LukasT03/LTS-Respooler/3D Files/STLs V4/Tension Holder 1.stl

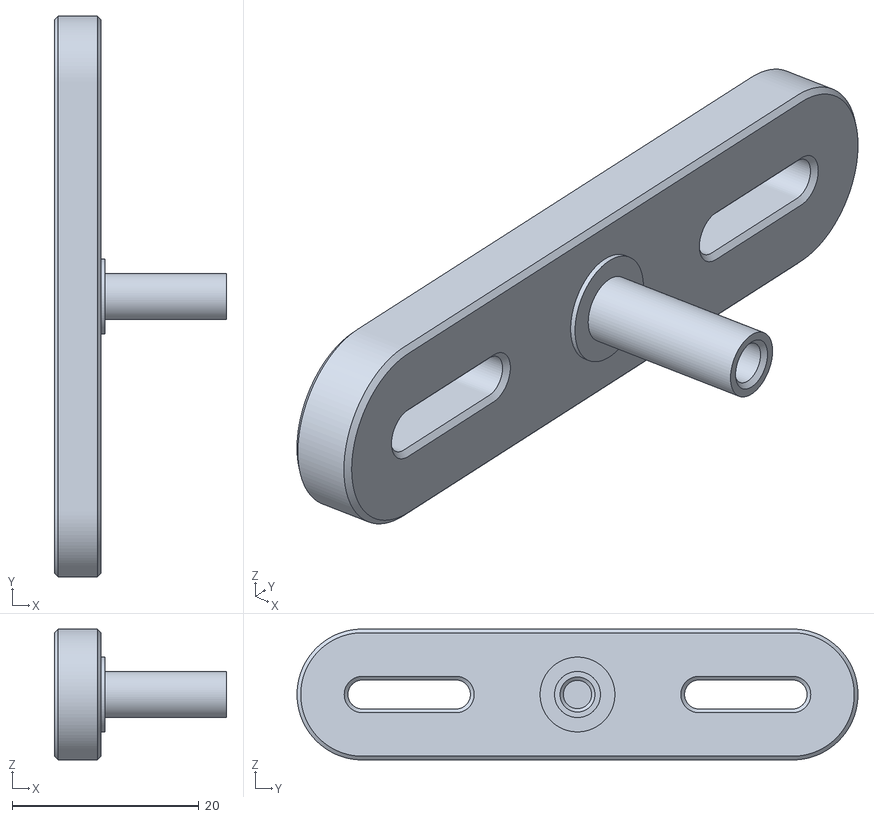
[picture p15: CAD file, 2025-08-27]
3D Files/STLs V4/Tension Holder 1.stl
18.4 x 60.0 x 14.0
