LukasT03/LTS-Respooler/Print Profiles/Control Panel (single color).3mf

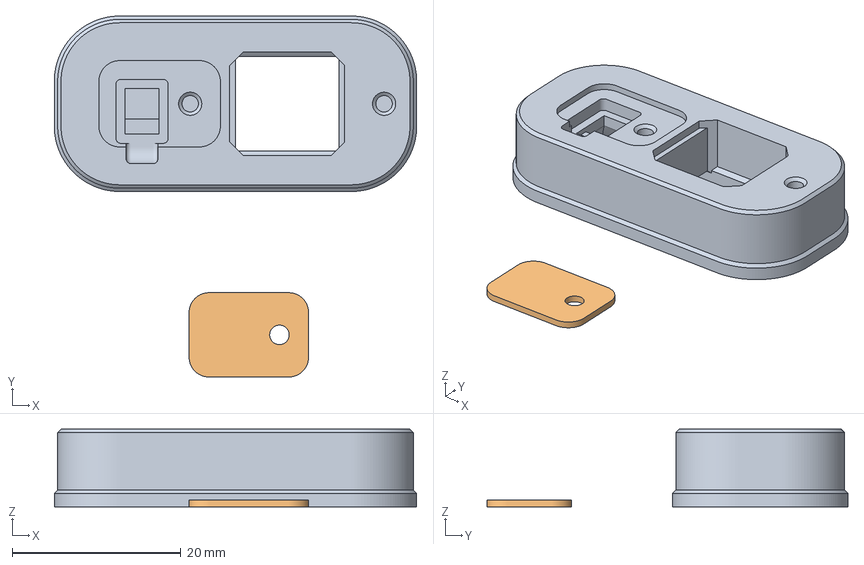
[picture p16: CAD file, 2025-09-30]
Print Profiles/Control Panel (single color).3mf
43.0 x 42.8 x 9.20 mm
Control Panel Single Color.stl
Control Panel Plate.stl
