LukasT03/LTS-Respooler/3D Files/STLs Pro/Control Panel Plate.stl

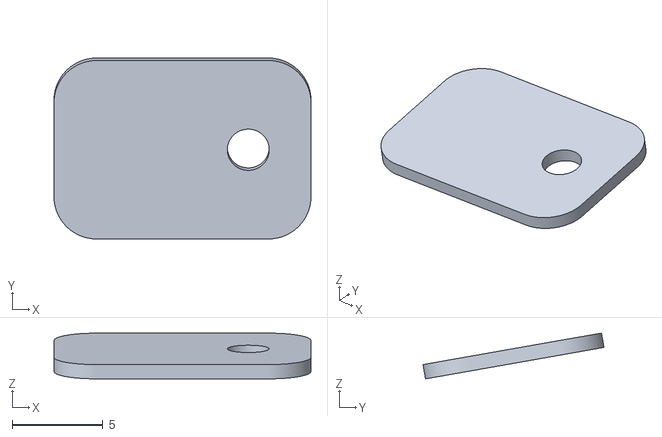
[picture p17: CAD file, 2025-09-09]
3D Files/STLs Pro/Control Panel Plate.stl
14.2 x 9.99 x 2.52
