LukasT03/LTS-Respooler/3D Files/STLs V4/Guide Pulley.stl

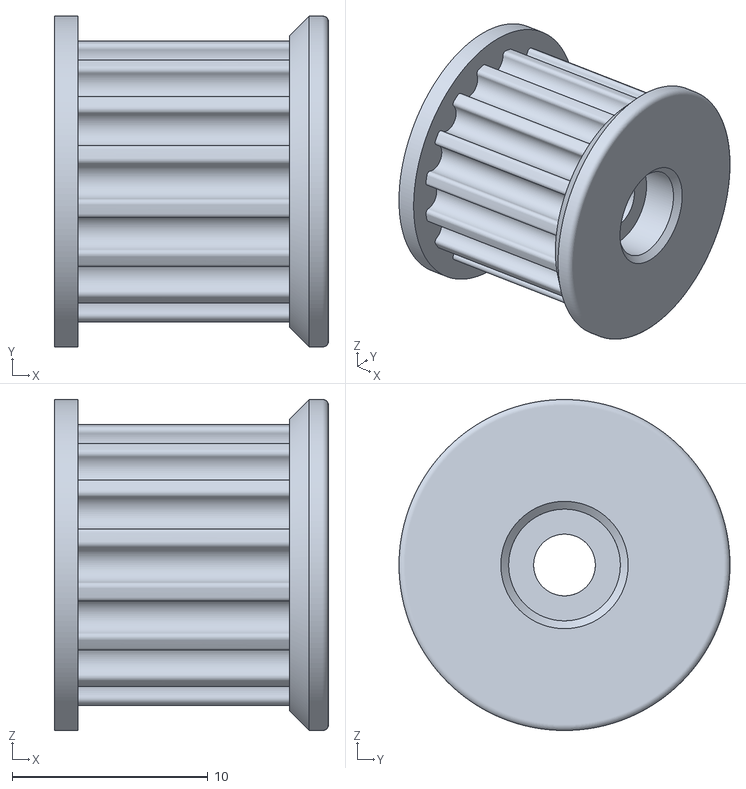
[picture p18: CAD file, 2025-08-24]
3D Files/STLs V4/Guide Pulley.stl
14.0 x 16.9 x 16.9
