LukasT03/LTS-Respooler/Print Profiles/LTS Respooler (V3).3mf

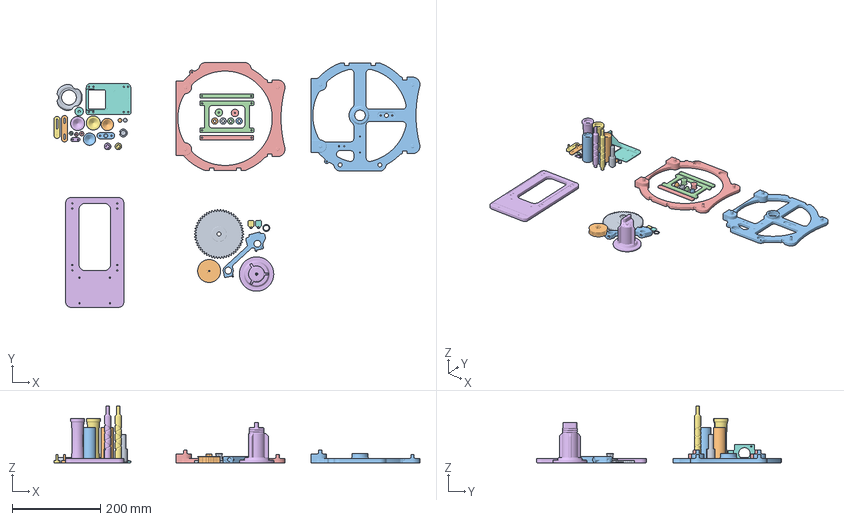
[picture p19: CAD file, 2025-08-23]
Print Profiles/LTS Respooler (V3).3mf
830.6 x 555.6 x 128.4 mm
Spool nut.stl
bottom Roller.stl x 2
Brace single.stl x 2
Spool center.stl
Filament guide lid.stl x 2
Filament guide pins.stl x 2
Filament guide.stl
Brace double.stl
Frame L.stl
Base.stl
top Roller.stl x 2
washer Spool shaft.stl
big Gear V3.stl
small Gear V3.stl
Frame R V3.stl
Guide Pulley V3.stl x 2
Worm gear V3.stl x 2
Motor Base V3.stl
Spool shaft V3.stl
Tension holder 1.stl
Gear shaft.stl
Tension washer 1.stl x 2
Tension washer 2.stl
Tension holder 2.stl
Motor Pulley.stl
Tension Pulley 1.stl x 2
Tension Pulley 2.stl x 2
Bearing washer.stl
