LukasT03/LTS-Respooler/3D Files/STLs Pro/Control Panel Multi Color 1.stl

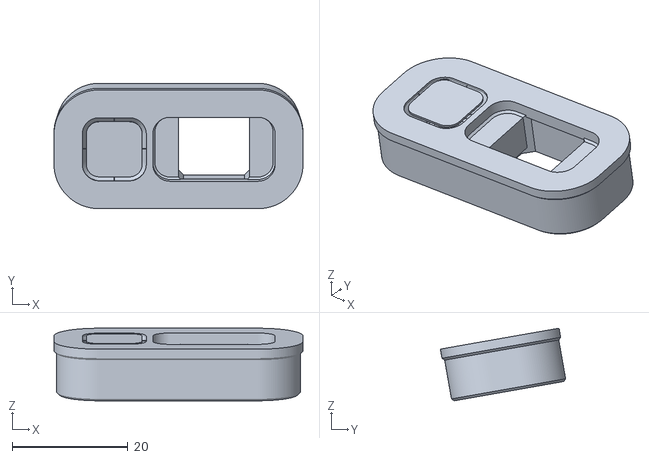
[picture p20: CAD file, 2025-09-09]
3D Files/STLs Pro/Control Panel Multi Color 1.stl
43.0 x 21.6 x 12.5
