LukasT03/LTS-Respooler/3D Files/STLs V4/Small Gear.stl

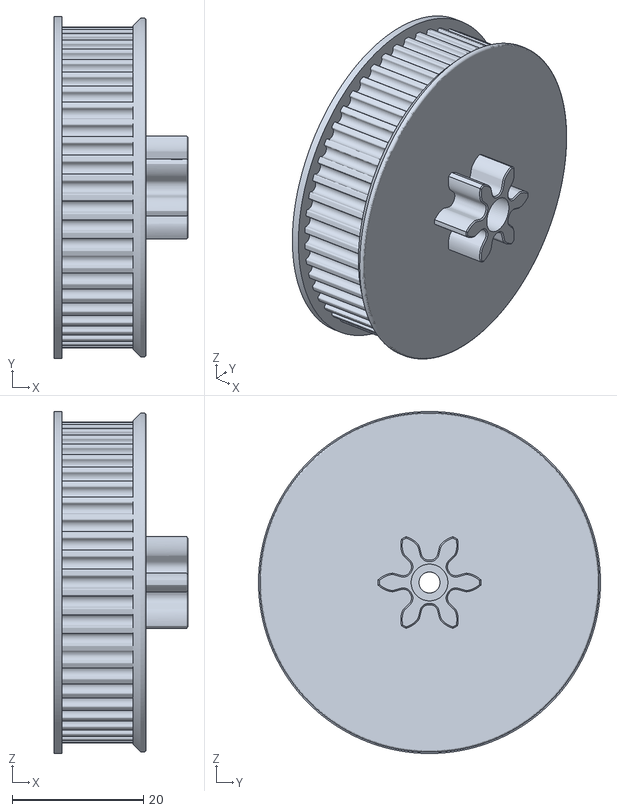
[picture p21: CAD file, 2025-08-24]
3D Files/STLs V4/Small Gear.stl
20.4 x 52.1 x 52.1
