LukasT03/LTS-Respooler/3D Files/STLs V4/Spool Shaft.stl

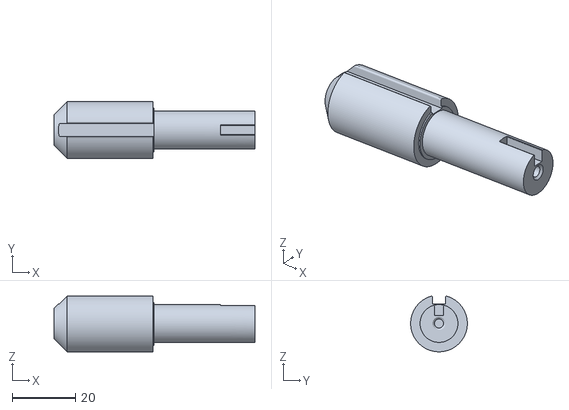
[picture p22: CAD file, 2025-08-24]
3D Files/STLs V4/Spool Shaft.stl
63.8 x 18.0 x 17.7
