LukasT03/LTS-Respooler/3D Files/STLs Pro/Tension Holder.stl

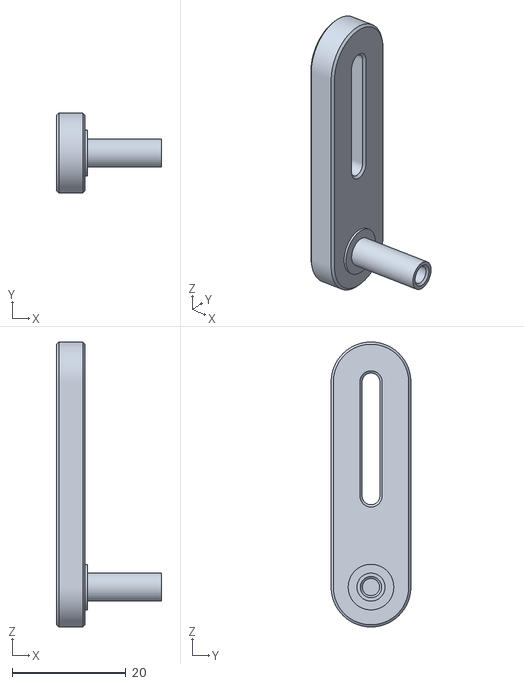
[picture p23: CAD file, 2025-08-27]
3D Files/STLs Pro/Tension Holder.stl
18.4 x 14.0 x 50.0
