LukasT03/LTS-Respooler/3D Files/STLs V4/Gear Shaft.stl

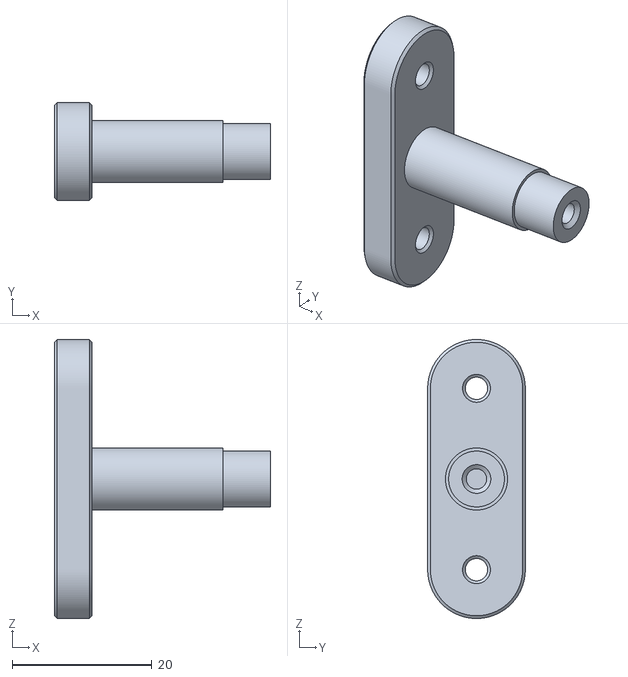
[picture p24: CAD file, 2025-08-24]
3D Files/STLs V4/Gear Shaft.stl
31.0 x 14.0 x 40.0
