LukasT03/LTS-Respooler/3D Files/STLs Pro/Motor Base.stl

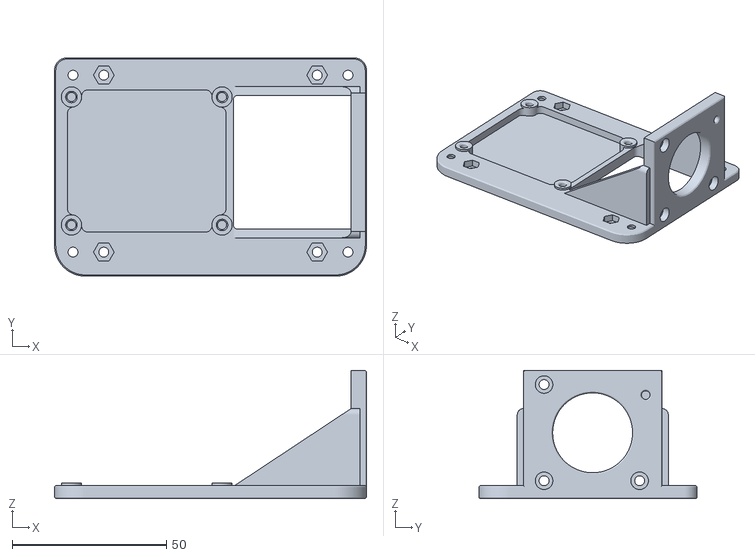
[picture p25: CAD file, 2025-08-25]
3D Files/STLs Pro/Motor Base.stl
101.2 x 70.8 x 41.6
