LukasT03/LTS-Respooler/3D Files/STLs Pro/Control Panel Button.stl

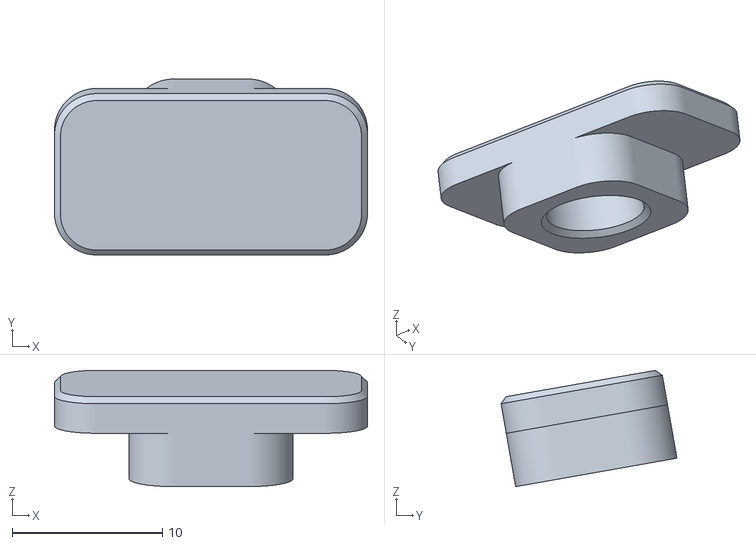
[picture p26: CAD file, 2025-08-25]
3D Files/STLs Pro/Control Panel Button.stl
20.8 x 11.7 x 7.73
