LukasT03/LTS-Respooler/3D Files/STLs V4/Filament Guide Lid.stl

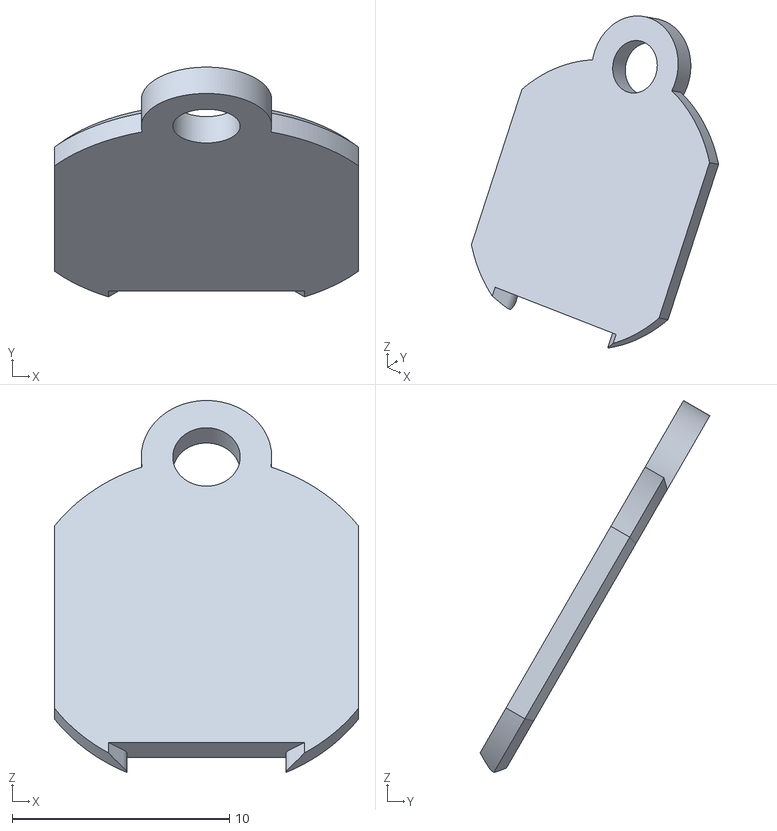
[picture p27: CAD file, 2025-08-24]
3D Files/STLs V4/Filament Guide Lid.stl
14.0 x 10.6 x 17.1
