LukasT03/LTS-Respooler/3D Files/STLs Pro/Top Roller.stl

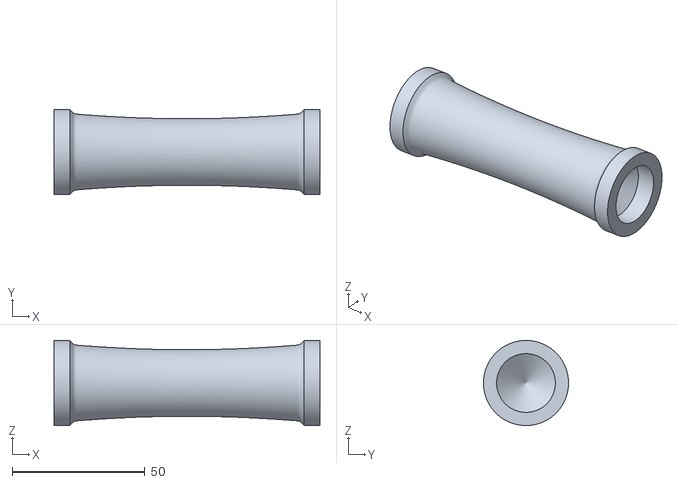
[picture p28: CAD file, 2025-08-24]
3D Files/STLs Pro/Top Roller.stl
100.0 x 32.0 x 32.0
