LukasT03/LTS-Respooler/3D Files/STLs V4/Big Gear.stl

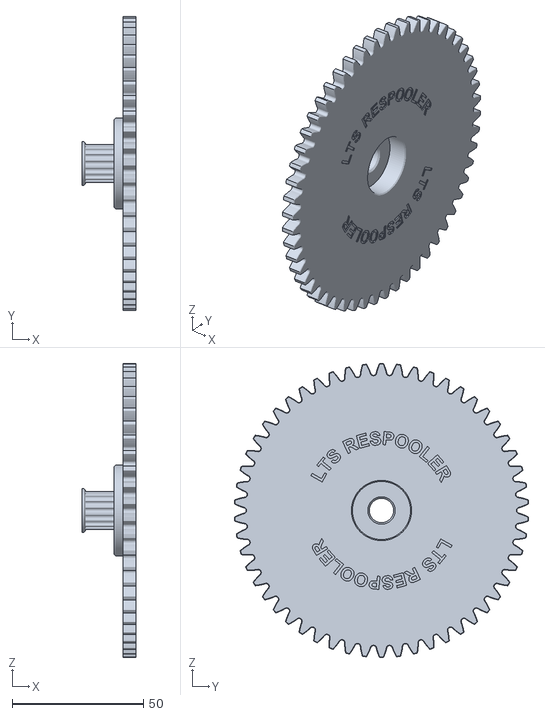
[picture p29: CAD file, 2025-08-24]
3D Files/STLs V4/Big Gear.stl
20.6 x 111.9 x 112.0
