LukasT03/LTS-Respooler/3D Files/STLs Pro/Brace Double.stl

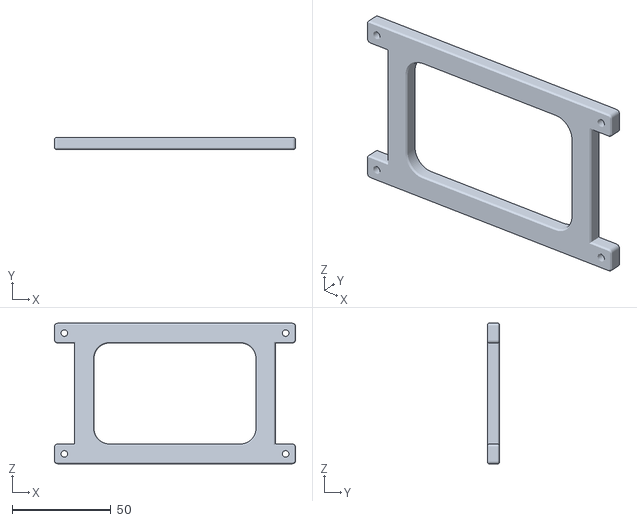
[picture p30: CAD file, 2025-08-24]
3D Files/STLs Pro/Brace Double.stl
122.0 x 6.00 x 71.1
