LukasT03/LTS-Respooler/3D Files/STLs Pro/Bottom Roller.stl

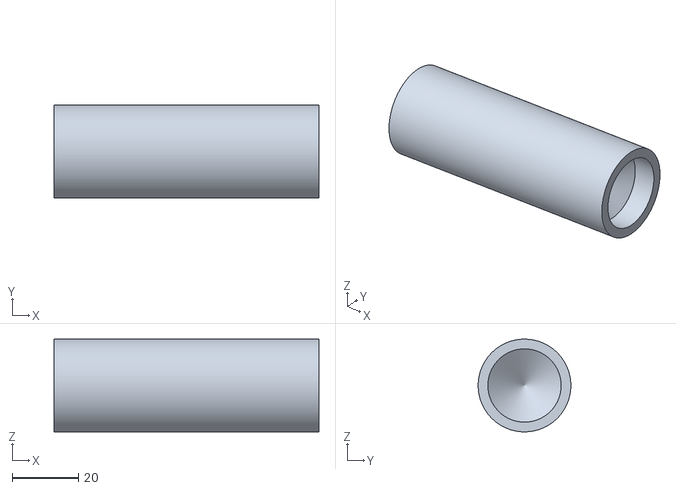
[picture p31: CAD file, 2025-08-24]
3D Files/STLs Pro/Bottom Roller.stl
80.0 x 28.0 x 28.0
