LukasT03/LTS-Respooler/3D Files/STLs Pro/Tension Pulley 2.stl

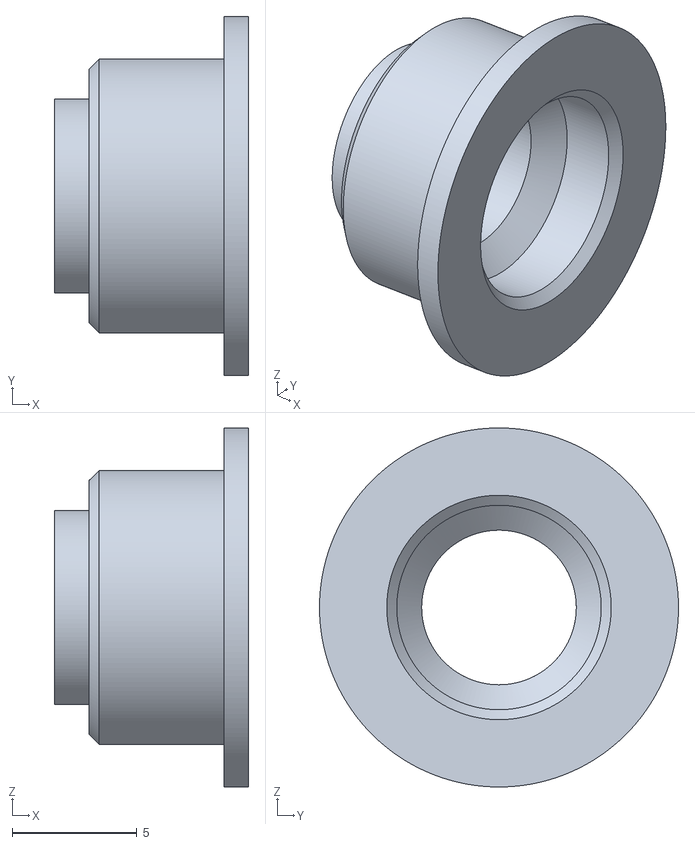
[picture p32: CAD file, 2025-08-24]
3D Files/STLs Pro/Tension Pulley 2.stl
7.80 x 14.4 x 14.4
