LukasT03/LTS-Respooler/3D Files/STLs Pro/Tension Pulley 1.stl

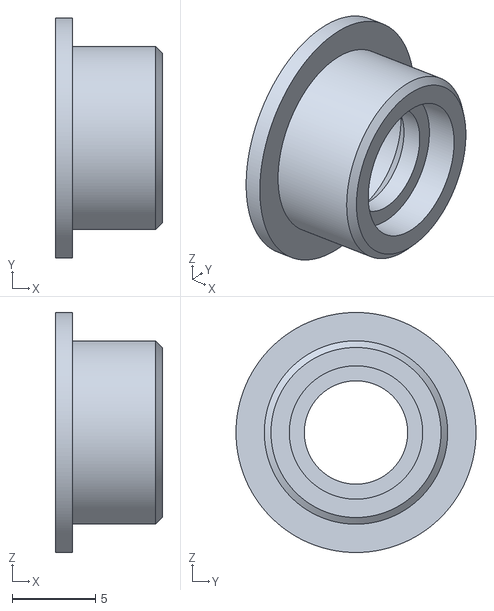
[picture p33: CAD file, 2025-08-24]
3D Files/STLs Pro/Tension Pulley 1.stl
6.40 x 14.4 x 14.4
