LukasT03/LTS-Respooler/3D Files/STLs Pro/Brace Single.stl

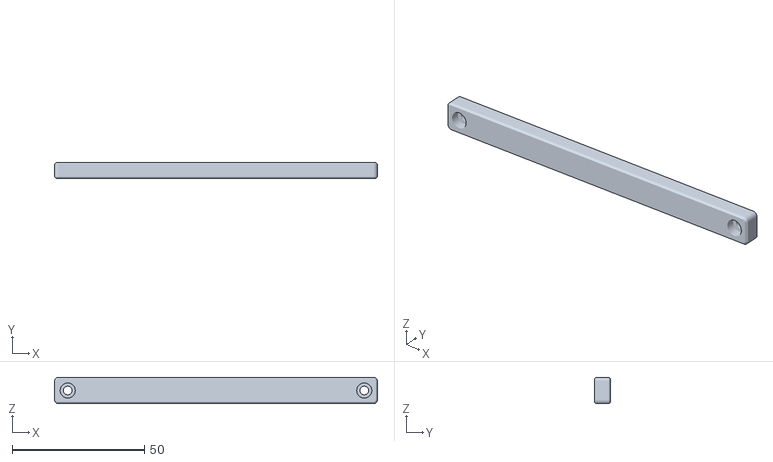
[picture p34: CAD file, 2025-08-24]
3D Files/STLs Pro/Brace Single.stl
122.0 x 6.00 x 10.0
