LukasT03/LTS-Respooler/3D Files/STLs Pro/TPU Foot 1.stl

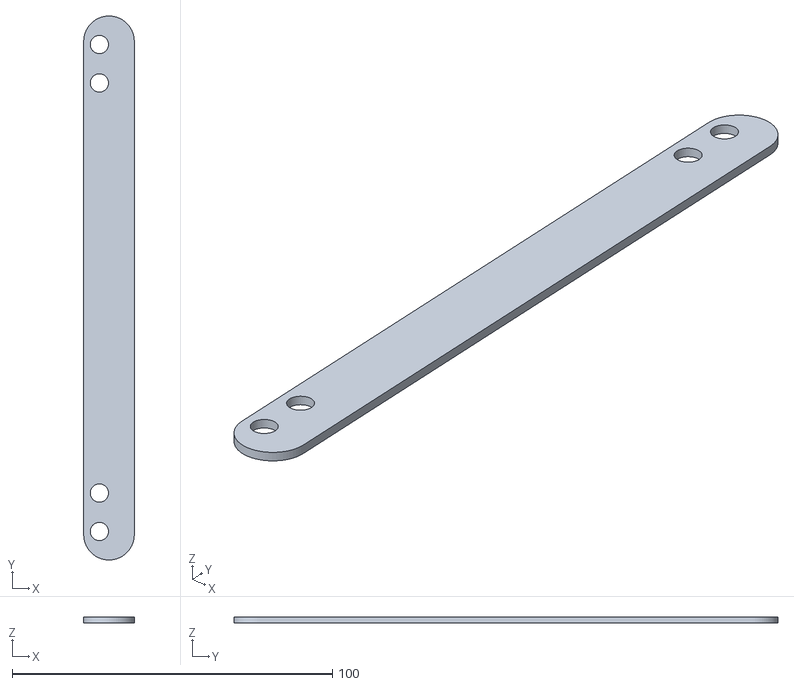
[picture p35: CAD file, 2025-08-24]
3D Files/STLs Pro/TPU Foot 1.stl
15.8 x 169.8 x 2.00
