LukasT03/LTS-Respooler/3D Files/STLs Pro/TPU Foot 2.stl

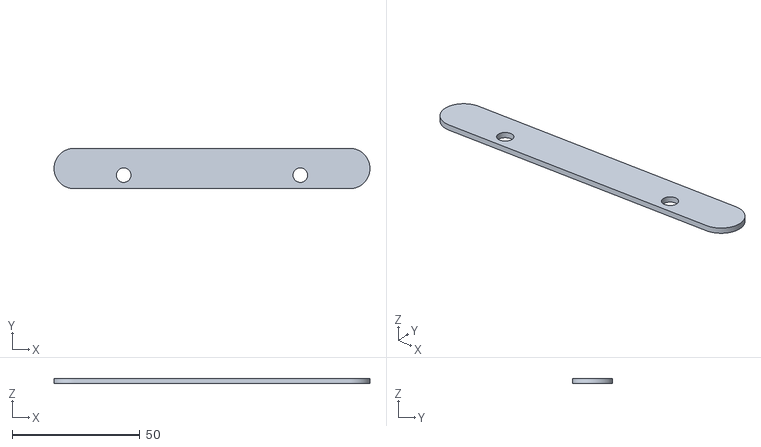
[picture p36: CAD file, 2025-08-24]
3D Files/STLs Pro/TPU Foot 2.stl
123.8 x 15.8 x 2.00
