LukasT03/LTS-Respooler/3D Files/STLs Pro/Motor Pulley.stl

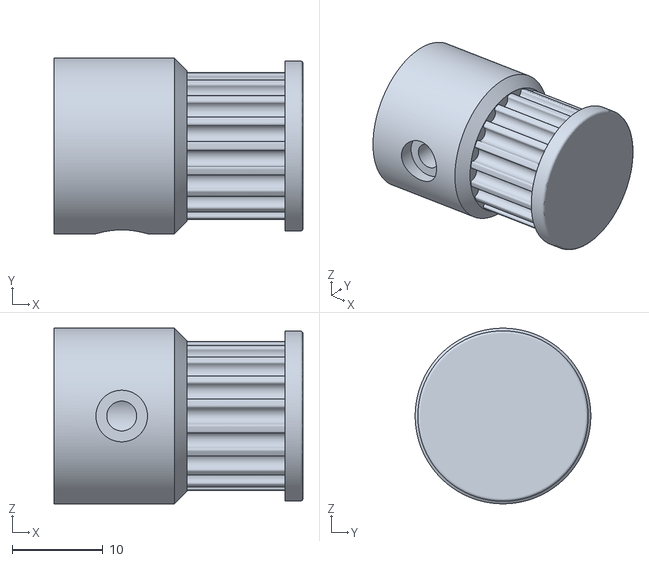
[picture p37: CAD file, 2025-08-24]
3D Files/STLs Pro/Motor Pulley.stl
27.5 x 19.4 x 19.4
